frank26080115/UsbXlater/UsbXlater_FW/btstack/src/bt_control.h

/*
 * Copyright (C) 2009-2012 by Matthias Ringwald
 *
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
 * 1. Redistributions of source code must retain the above copyright
 *    notice, this list of conditions and the following disclaimer.
 * 2. Redistributions in binary form must reproduce the above copyright
 *    notice, this list of conditions and the following disclaimer in the
 *    documentation and/or other materials provided with the distribution.
 * 3. Neither the name of the copyright holders nor the names of
 *    contributors may be used to endorse or promote products derived
 *    from this software without specific prior written permission.
 * 4. Any redistribution, use, or modification is done solely for
 *    personal benefit and not for any commercial purpose or for
 *    monetary gain.
 *
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
 * Please inquire about commercial licensing options at btstack@ringwald.ch
 *
 */

/*
 *  bt_control.h
 *
 *  BT Control API -- allows BT Daemon to initialize and control differnt hardware
 *
 *  Created by Matthias Ringwald on 5/19/09.
 *
 */

#ifndef __BT_CONTROL_H
#define __BT_CONTROL_H

#include <stdint.h>

#if defined __cplusplus
extern "C" {
#endif

typedef enum {
    POWER_WILL_SLEEP = 1,
    POWER_WILL_WAKE_UP
} POWER_NOTIFICATION_t;

typedef enum {
	NO_PACKET_RUN_DEFAULT_INIT,
	NO_PACKET_SKIP_INIT,
	NO_PACKET_GET_NEXT_CMD,
	SENT_PACKET_GET_NEXT_CMD,
	SENT_PACKET_RUN_DEFAULT_INIT,
	SENT_PACKET_SKIP_INIT,
} CMD_ACTION_t;

typedef struct {
    int          (*on)   (void *config);  // <-- turn BT module on and configure
    int          (*off)  (void *config);  // <-- turn BT module off
    int          (*sleep)(void *config);  // <-- put BT module to sleep    - only to be called after ON
    int          (*wake) (void *config);  // <-- wake BT module from sleep - only to be called after SLEEP
    int          (*valid)(void *config);  // <-- test if hardware can be supported
    const char * (*name) (void *config);  // <-- return hardware name

    /** support for UART baud rate changes - cmd has to be stored in hci_cmd_buffer
     * @return have command
     */
    int          (*baudrate_cmd)(void * config, uint32_t baudrate, uint8_t *hci_cmd_buffer); 
    
    /** support custom init sequences after RESET command - cmd has to be stored in hci_cmd_buffer
      * @return have command
      */
    CMD_ACTION_t (*next_cmd)(void * obj, uint8_t * hci_cmd_buffer);

    void         (*register_for_power_notifications)(void (*cb)(POWER_NOTIFICATION_t event));

    void         (*hw_error)(void); 
} bt_control_t;

#if defined __cplusplus
}
#endif

#endif // __BT_CONTROL_H
