frank26080115/UsbXlater/UsbXlater_FW/ds4_emu_data.c

#include <stdint.h>
#include "ds4_emu.h"

const uint8_t ps4_sdp_service_search_attribute_response[PS4_SDP_SERVICE_SEARCH_ATTRIBUTE_RESPONSE_SIZE] = {
	//0x36, 0x01, 0x4d,
	0x36, 0x00, 0x32, 0x09, 0x00, 0x00, 0x0a, 0x00, 0x01, 0x00, 0x05, 0x09, 0x00,
	0x01, 0x35, 0x03, 0x19, 0x11, 0x0a, 0x09, 0x00, 0x04, 0x35, 0x10, 0x35, 0x06, 0x19, 0x01, 0x00,
	0x09, 0x00, 0x19, 0x35, 0x06, 0x19, 0x00, 0x19, 0x09, 0x01, 0x02, 0x09, 0x00, 0x09, 0x35, 0x08,
	0x35, 0x06, 0x19, 0x11, 0x0d, 0x09, 0x01, 0x02, 0x36, 0x00, 0x32, 0x09, 0x00, 0x00, 0x0a, 0x00,
	0x01, 0x00, 0x06, 0x09, 0x00, 0x01, 0x35, 0x03, 0x19, 0x11, 0x0b, 0x09, 0x00, 0x04, 0x35, 0x10,
	0x35, 0x06, 0x19, 0x01, 0x00, 0x09, 0x00, 0x19, 0x35, 0x06, 0x19, 0x00, 0x19, 0x09, 0x01, 0x02,
	0x09, 0x00, 0x09, 0x35, 0x08, 0x35, 0x06, 0x19, 0x11, 0x0d, 0x09, 0x01, 0x02, 0x36, 0x00, 0x3b,
	0x09, 0x00, 0x00, 0x0a, 0x00, 0x01, 0x00, 0x07, 0x09, 0x00, 0x01, 0x35, 0x06, 0x19, 0x11, 0x0e,
	0x19, 0x11, 0x0f, 0x09, 0x00, 0x04, 0x35, 0x10, 0x35, 0x06, 0x19, 0x01, 0x00, 0x09, 0x00, 0x17,
	0x35, 0x06, 0x19, 0x00, 0x17, 0x09, 0x01, 0x03, 0x09, 0x00, 0x09, 0x35, 0x08, 0x35, 0x06, 0x19,
	0x11, 0x0e, 0x09, 0x01, 0x04, 0x09, 0x03, 0x11, 0x09, 0x00, 0x02, 0x36, 0x00, 0x4d, 0x09, 0x00,
	0x00, 0x0a, 0x00, 0x01, 0x00, 0x08, 0x09, 0x00, 0x01, 0x35, 0x03, 0x19, 0x11, 0x0c, 0x09, 0x00,
	0x04, 0x35, 0x10, 0x35, 0x06, 0x19, 0x01, 0x00, 0x09, 0x00, 0x17, 0x35, 0x06, 0x19, 0x00, 0x17,
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
};

const uint8_t ps4_sdp_service_search_pattern[] = {
	0x35, 0x03, 0x19, 0x01, 0x00,
};

const uint8_t ps4_sdp_attribute_id_list[] = {
	0x35, 0x05, 0x0A, 0x00, 0x00, 0xFF, 0xFF
};

const uint8_t ds4_link_key[] = { 0, 1, 2, 3, 4, 5, 6, 7, 8, 9, 0xA, 0xB, 0xC, 0xD, 0xE, 0xF };
